thingSoC/TSOC_RS485_EM/TSOC_RS485_EM/eagleUp/eagleUp_TSOC_RS485_EM_board_top.jpg

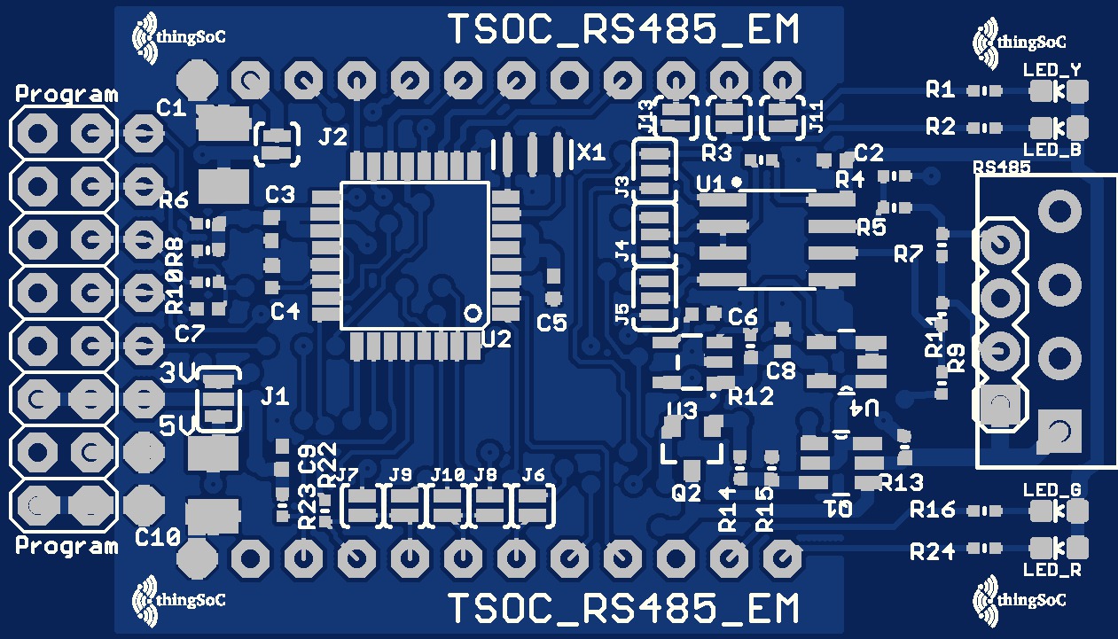
TSOC_RS485_EM/eagleUp/eagleUp_TSOC_RS485_EM_board_top.jpg
